ketszim97/USB_PD_Sink/Renders/Fusion_Render_4.png

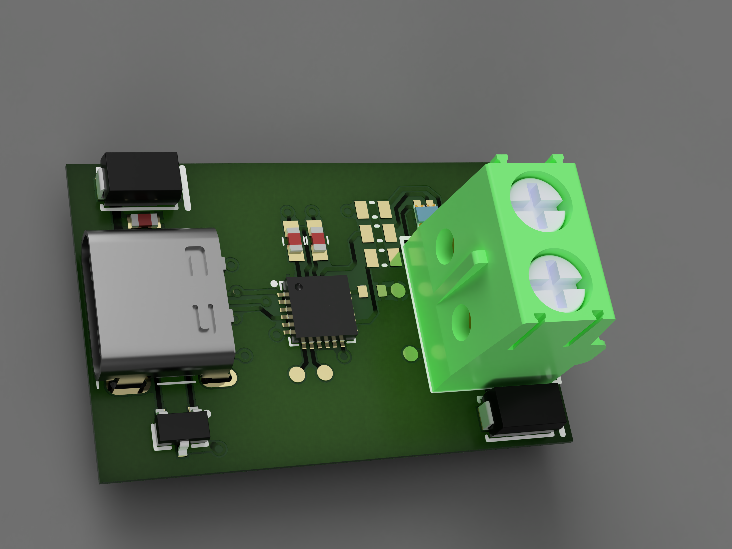
Renders/Fusion_Render_4.png
