ketszim97/USB_PD_Sink/Renders/Fusion_Render_11.png

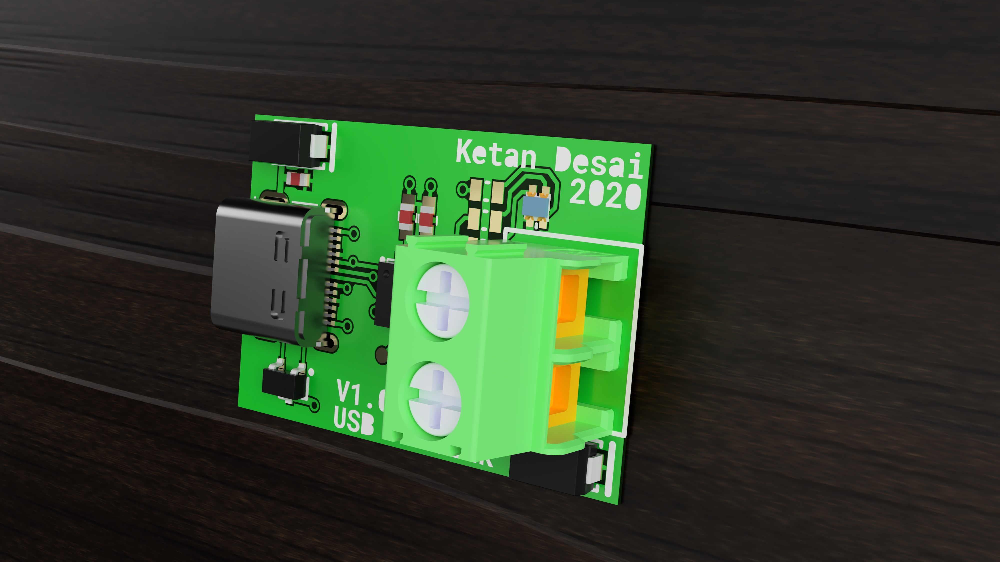
Renders/Fusion_Render_11.png
