ketszim97/USB_PD_Sink/Renders/Fusion_Render_12.png

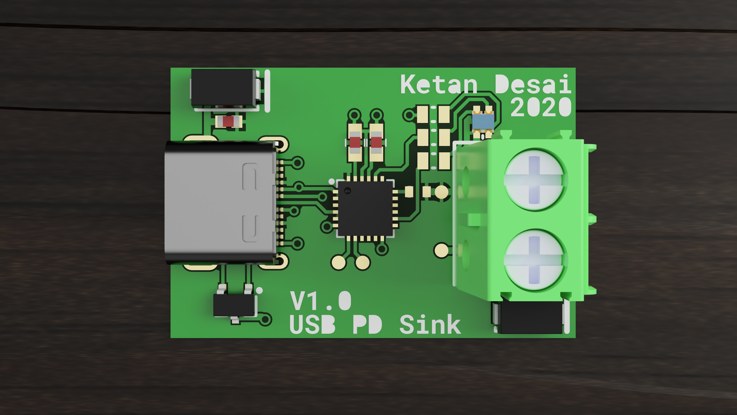
Renders/Fusion_Render_12.png
